danielei9/environmentalSensor_HW/tests/EXAMPLE LORA/src/ioold.cpp

// // -*- mode: c++ -*-

// // --------------------------------------------------------------
// // Autor: Daniel Burruchaga Sola
// // Date: 03 - 12 - 2021
// // Name: Example LORA 
// // Description: Lora Test 
// // Se encarga de Realizar join con gateway lora y envio de datos 
// // --------------------------------------------------------------
// #define CFG_sx1276_radio 1 // HPD13A LoRa SoC

// #include <Arduino.h>
// #include <lmic.h>
// #include <hal/hal.h>
// #include <SPI.h>
// #include <loraLib.hpp>
// void do_send(osjob_t* j);

// // APPEUI
// #define APPEUI_DEF                                     \
//     {                                                  \
//         0x64, 0x47, 0x1d, 0xa3, 0xe1, 0x71, 0x99, 0x13 \
//     }
// // DEVEUI
// #define DEVEUI_DEF                                     \
//     {                                                  \
//         0x64, 0x47, 0x1d, 0xa3, 0xe1, 0x71, 0x99, 0x13 \
//     }
// // APPKEY
// #define APPKEY_DEF                                                                                     \
//     {                                                                                                  \
//         0xd6, 0x37, 0xf7, 0x50, 0xc3, 0xa7, 0xc2, 0x25, 0x21, 0xdc, 0x53, 0x27, 0x19, 0xaa, 0x6c, 0x53 \
//     }
// static const u1_t PROGMEM APPEUI[8]=  {                                                  \
//         0x64, 0x47, 0x1d, 0xa3, 0xe1, 0x71, 0x99, 0x13 \
//     };

// void os_getArtEui (u1_t* buf) { memcpy_P(buf, APPEUI, 8);}
// // This should also be in little endian format, see above.
// static const u1_t PROGMEM DEVEUI[8]={ 0x64, 0x47, 0x1d, 0xa3, 0xe1, 0x71, 0x99, 0x13};
// void os_getDevEui (u1_t* buf) { memcpy_P(buf, DEVEUI, 8);}

// static const u1_t PROGMEM APPKEY[16] = {  0xd6, 0x37, 0xf7, 0x50, 0xc3, 0xa7, 0xc2, 0x25, 0x21, 0xdc, 0x53, 0x27, 0x19, 0xaa, 0x6c, 0x53 };
// void os_getDevKey (u1_t* buf) {  memcpy_P(buf, APPKEY, 16);}

// static uint8_t mydata[] = "Hello, world!";
// static osjob_t sendjob;
// const unsigned TX_INTERVAL = 60;

// // Pin mapping
// const lmic_pinmap lmic_pins = {
//     .nss = 5,
//     .rxtx = LMIC_UNUSED_PIN,
//     .rst = 14,
//     .dio = {2, 3, 4},
// };

// /**
//      * print hex received
//      * @param v index to print
//      */
// void printHex2(unsigned v) {
//     v &= 0xff;
//     if (v < 16)
//         Serial.print('0');
//     Serial.print(v, HEX);
// }

// /**
//      * Schedule events on the OS
//      * @param ev event ocurred in the os
//      */
// void onEvent (ev_t ev) {
//     Serial.print(os_getTime());
//     Serial.print(": ");
//     switch(ev) {
//         case EV_SCAN_TIMEOUT:
//             Serial.println(F("EV_SCAN_TIMEOUT"));
//             break;
//         case EV_BEACON_FOUND:
//             Serial.println(F("EV_BEACON_FOUND"));
//             break;
//         case EV_BEACON_MISSED:
//             Serial.println(F("EV_BEACON_MISSED"));
//             break;
//         case EV_BEACON_TRACKED:
//             Serial.println(F("EV_BEACON_TRACKED"));
//             break;
//         case EV_JOINING:
//             Serial.println(F("EV_JOINING"));
//             break;
//         case EV_JOINED:
//             Serial.println(F("EV_JOINED"));
//             /*{
//               u4_t netid = 0;
//               devaddr_t devaddr = 0;
//               u1_t nwkKey[16];
//               u1_t artKey[16];
//              // LMIC_getSessionKeys(&netid, &devaddr, nwkKey, artKey);
//               Serial.print("netid: ");
//               Serial.println(netid, DEC);
//               Serial.print("devaddr: ");
//               Serial.println(devaddr, HEX);
//               Serial.print("AppSKey: ");
//               for (size_t i=0; i<sizeof(artKey); ++i) {
//                 if (i != 0)
//                   Serial.print("-");
//                 printHex2(artKey[i]);
//               }
//               Serial.println("");
//               Serial.print("NwkSKey: ");
//               for (size_t i=0; i<sizeof(nwkKey); ++i) {
//                       if (i != 0)
//                               Serial.print("-");
//                       printHex2(nwkKey[i]);
//               }
//               Serial.println();
//             }*/
//             // Disable link check validation (automatically enabled
//             // during join, but because slow data rates change max TX
// 	    // size, we don't use it in this example.
//             LMIC_setLinkCheckMode(0);
//             break;
//         /*
//         || This event is defined but not used in the code. No
//         || point in wasting codespace on it.
//         ||
//         || case EV_RFU1:
//         ||     Serial.println(F("EV_RFU1"));
//         ||     break;
//         */
//         case EV_JOIN_FAILED:
//             Serial.println(F("EV_JOIN_FAILED"));
//             break;
//         case EV_REJOIN_FAILED:
//             Serial.println(F("EV_REJOIN_FAILED"));
//             break;
//         case EV_TXCOMPLETE:
//             Serial.println(F("EV_TXCOMPLETE (includes waiting for RX windows)"));
//             if (LMIC.txrxFlags & TXRX_ACK)
//               Serial.println(F("Received ack"));
//             if (LMIC.dataLen) {
//               Serial.print(F("Received "));
//               Serial.print(LMIC.dataLen);
//               Serial.println(F(" bytes of payload"));
//             }
//             // Schedule next transmission
//            // os_setTimedCallback(&sendjob, os_getTime()+sec2osticks(TX_INTERVAL), do_send);
//             break;
//         case EV_LOST_TSYNC:
//             Serial.println(F("EV_LOST_TSYNC"));
//             break;
//         case EV_RESET:
//             Serial.println(F("EV_RESET"));
//             break;
//         case EV_RXCOMPLETE:
//             // data received in ping slot
//             Serial.println(F("EV_RXCOMPLETE"));
//             break;
//         case EV_LINK_DEAD:
//             Serial.println(F("EV_LINK_DEAD"));
//             break;
//         case EV_LINK_ALIVE:
//             Serial.println(F("EV_LINK_ALIVE"));
//             break;
//         /*
//         || This event is defined but not used in the code. No
//         || point in wasting codespace on it.
//         ||
//         || case EV_SCAN_FOUND:
//         ||    Serial.println(F("EV_SCAN_FOUND"));
//         ||    break;
//         */
//         case EV_TXSTART:
//             Serial.println(F("EV_TXSTART"));
//             break;
//         case EV_TXCANCELED:
//             Serial.println(F("EV_TXCANCELED"));
//             break;
//         case EV_RXSTART:
//             /* do not print anything -- it wrecks timing */
//             break;
//         case EV_JOIN_TXCOMPLETE:
//             Serial.println(F("EV_JOIN_TXCOMPLETE: no JoinAccept"));
//             break;

//         default:
//             Serial.print(F("Unknown event: "));
//             Serial.println((unsigned) ev);
//             break;
//     }
// }

// /**
//      * create a job to send data 
//      * @param j osjob to create the transmission
//      * @param data data arr pointer 
//      * @param port lora port to send
//      * @param size Data to send size
//      */
// void do_send(osjob_t* j,uint8_t *data, unsigned int port, unsigned int size){
//     // Check if there is not a current TX/RX job running
//     if (LMIC.opmode & OP_TXRXPEND) {
//         Serial.println(F("OP_TXRXPEND, not sending"));
//     } else {
//         // Prepare upstream data transmission at the next possible time.
//         LMIC_setTxData2(port, data, size-1,1);
//         Serial.println(F("Packet queued"));
//     }
//     // Next TX is scheduled after TX_COMPLETE event.
// }

// void setup() {
//     Serial.begin(9600);
//     Serial.println(F("Starting"));

//     #ifdef VCC_ENABLE
//     // For Pinoccio Scout boards
//     pinMode(VCC_ENABLE, OUTPUT);
//     digitalWrite(VCC_ENABLE, HIGH);
//     delay(1000);
//     #endif

//     // LMIC init
//     os_init();
//     // Reset the MAC state. Session and pending data transfers will be discarded.
//     LMIC_reset();

//     // Start job (sending automatically starts OTAA too)
//     do_send(&sendjob,mydata,3,sizeof(mydata));
// }
// unsigned long mill = 0;

// /**
//      * create a counter with millis
//      * @param lastmillis_ last time
//      * @param interval time interval to return true
//      */
// bool timerTrue(unsigned long lastmillis_, int interval)
// {
//     if (millis() > (lastmillis_ + interval))
//         return true;

//     return false;
// }

// void loop() {
//     os_runloop_once();
//        if (timerTrue(mill, 20000))
//         {
//     do_send(&sendjob,mydata,3,sizeof(mydata));
//             mill = millis();
//         }
// }
